ASMotionLab/Arduino-vMix-tally/Pictures/P1070470.jpg

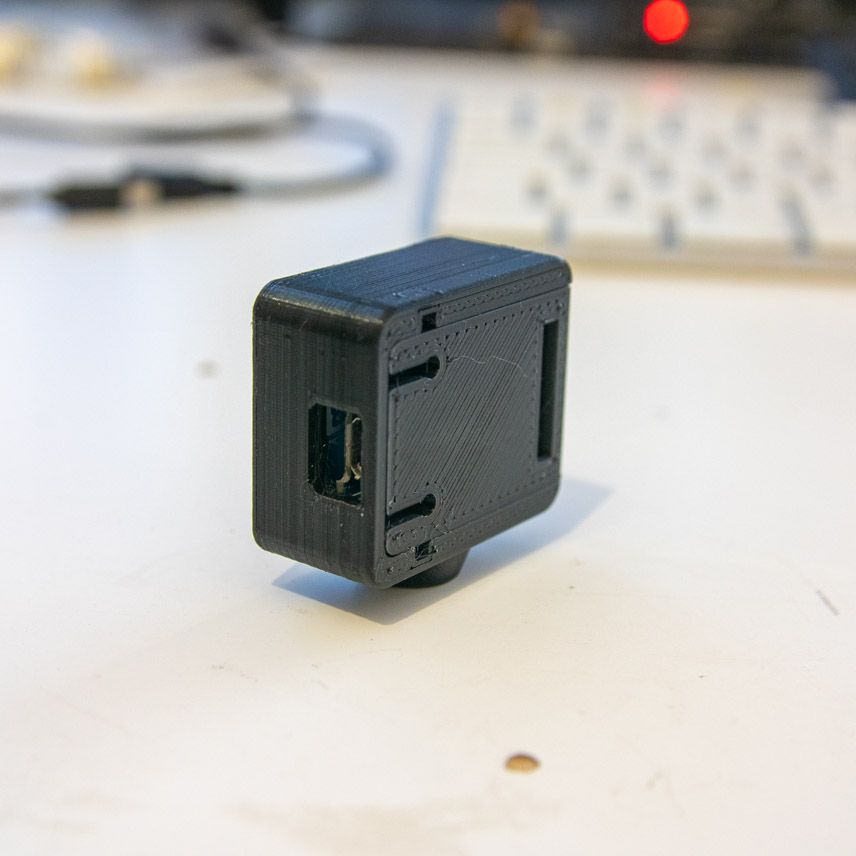
Pictures/P1070470.jpg
