ASMotionLab/Arduino-vMix-tally/Pictures/P1070475.jpg

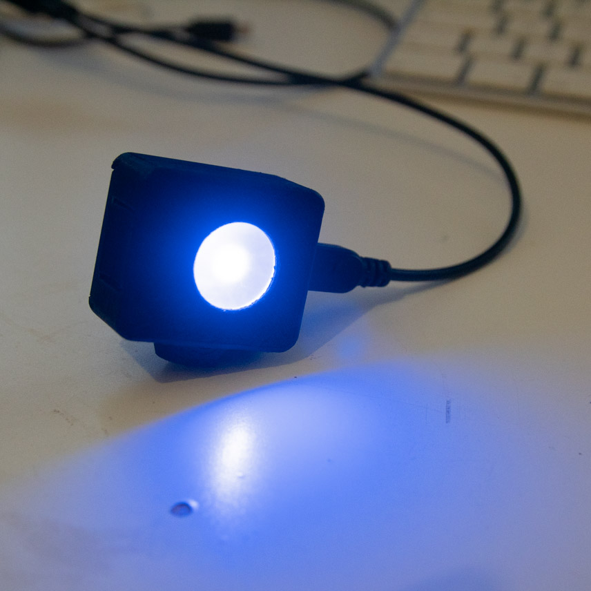
Pictures/P1070475.jpg
